AshuDas503/H-CUBE-Smartwatch/images/3D BOTTOM.png

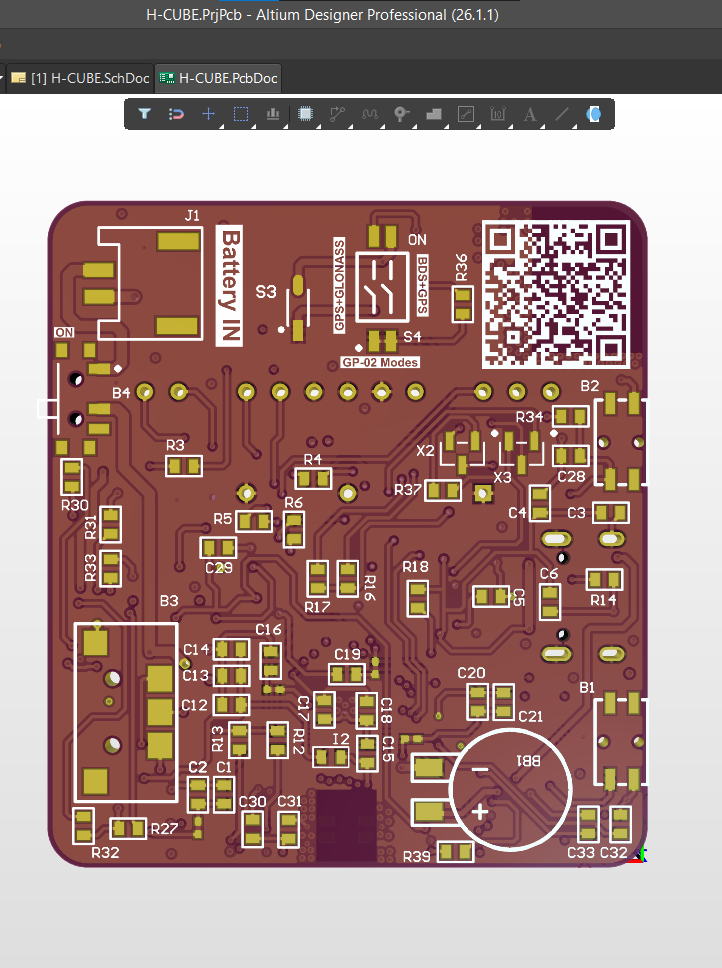
images/3D BOTTOM.png
