AshuDas503/H-CUBE-Smartwatch/images/Layer 1.png

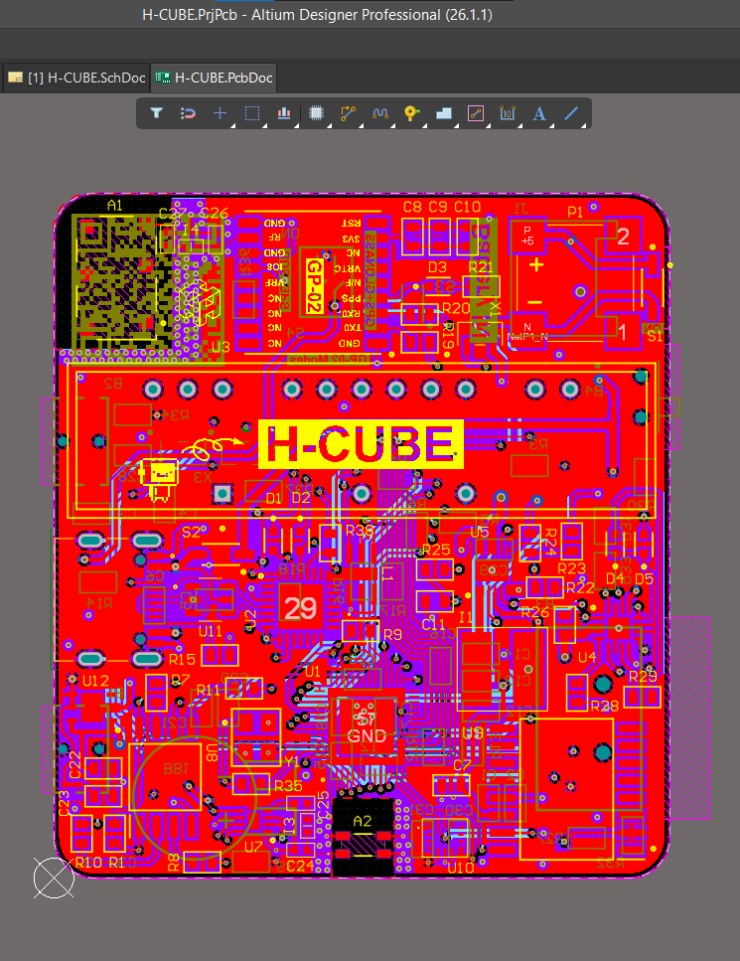
images/Layer 1.png
