AshuDas503/H-CUBE-Smartwatch/images/Layer 2.png

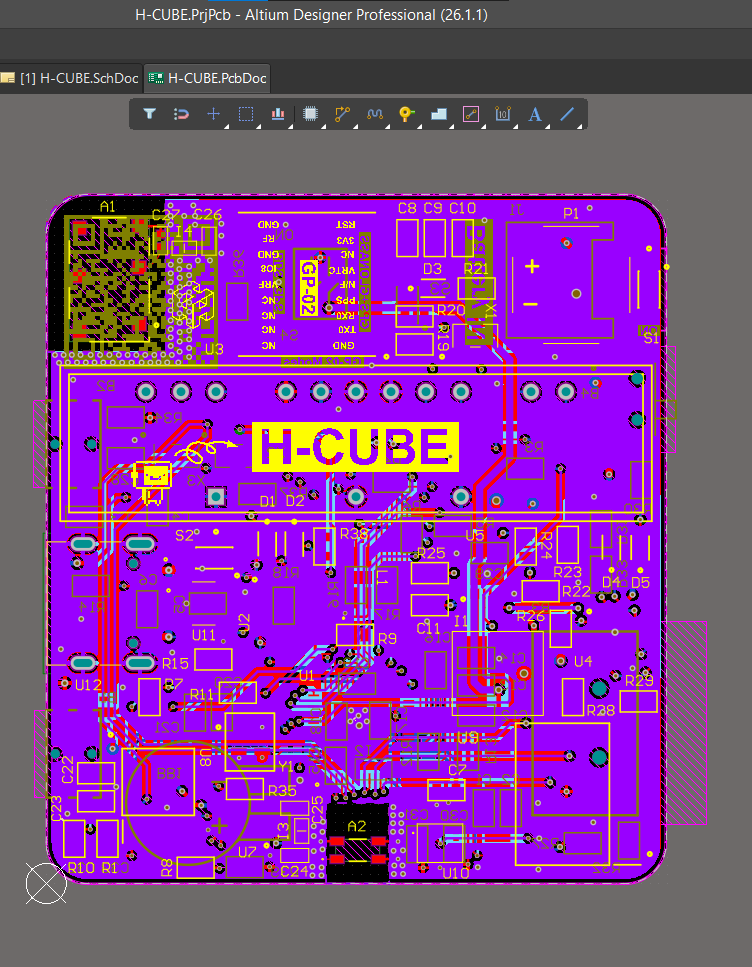
images/Layer 2.png
