AshuDas503/H-CUBE-Smartwatch/images/Layer 3.png

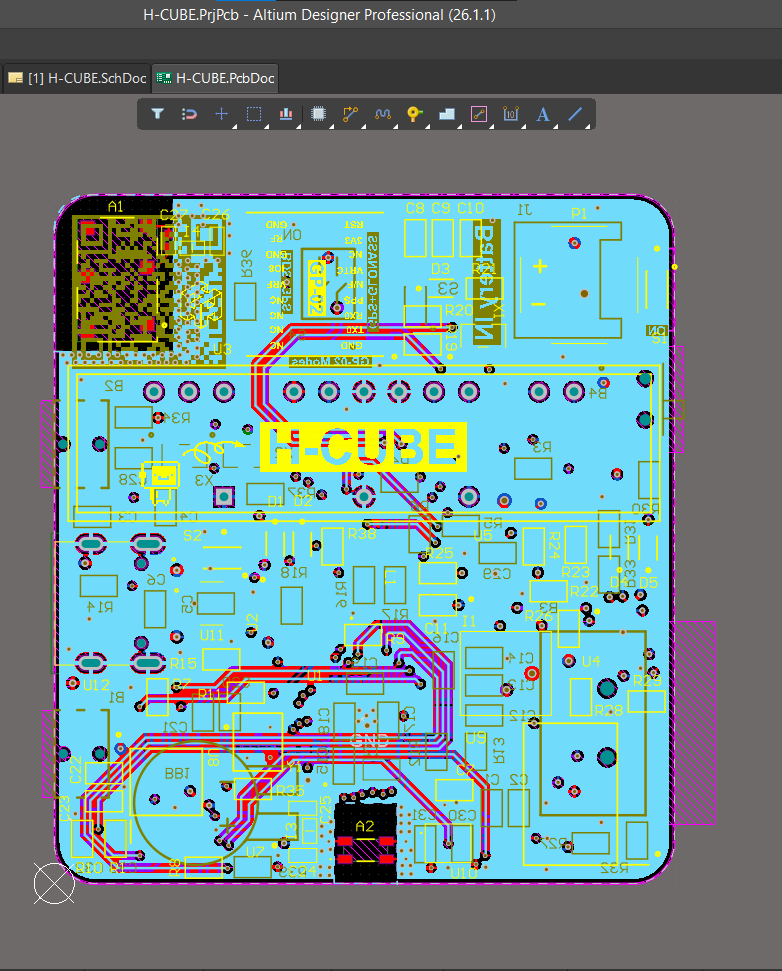
images/Layer 3.png
