AshuDas503/H-CUBE-Smartwatch/images/PCB View2.jpg

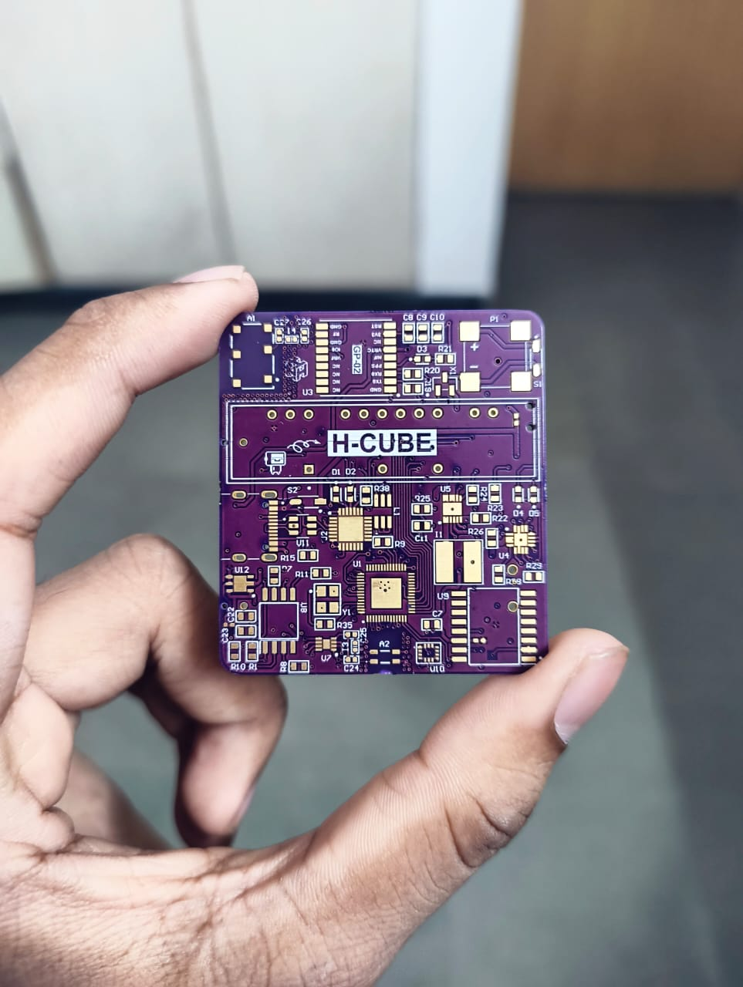
images/PCB View2.jpg
