AshuDas503/H-CUBE-Smartwatch/images/3D view with component Bottom.png

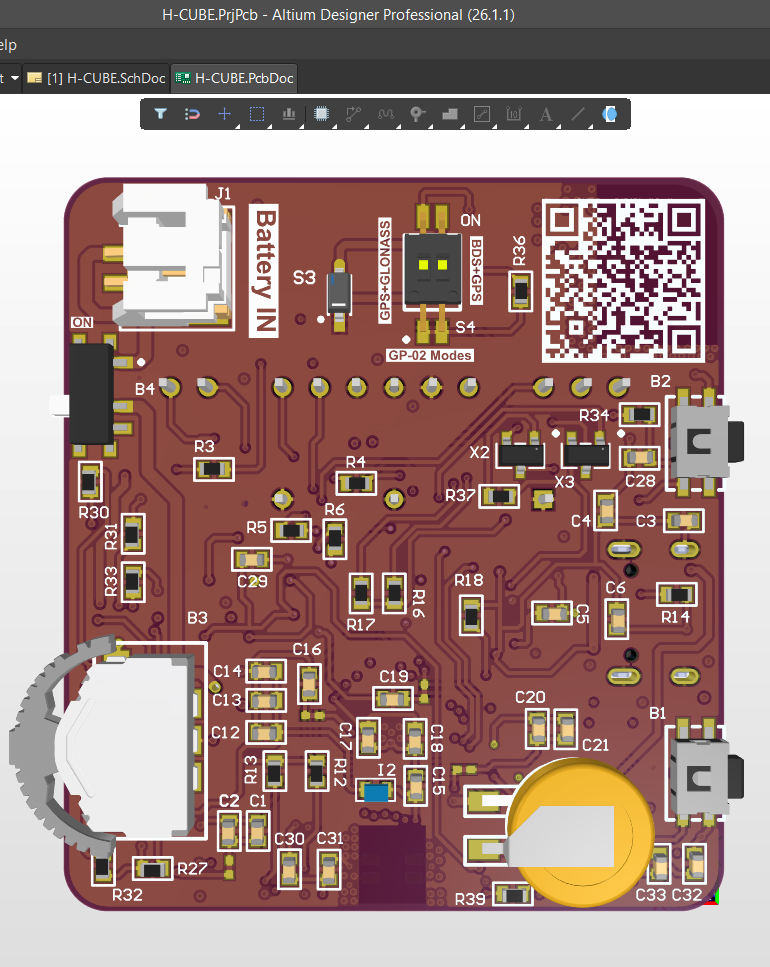
images/3D view with component Bottom.png
