AshuDas503/H-CUBE-Smartwatch/images/3d view with components top.png

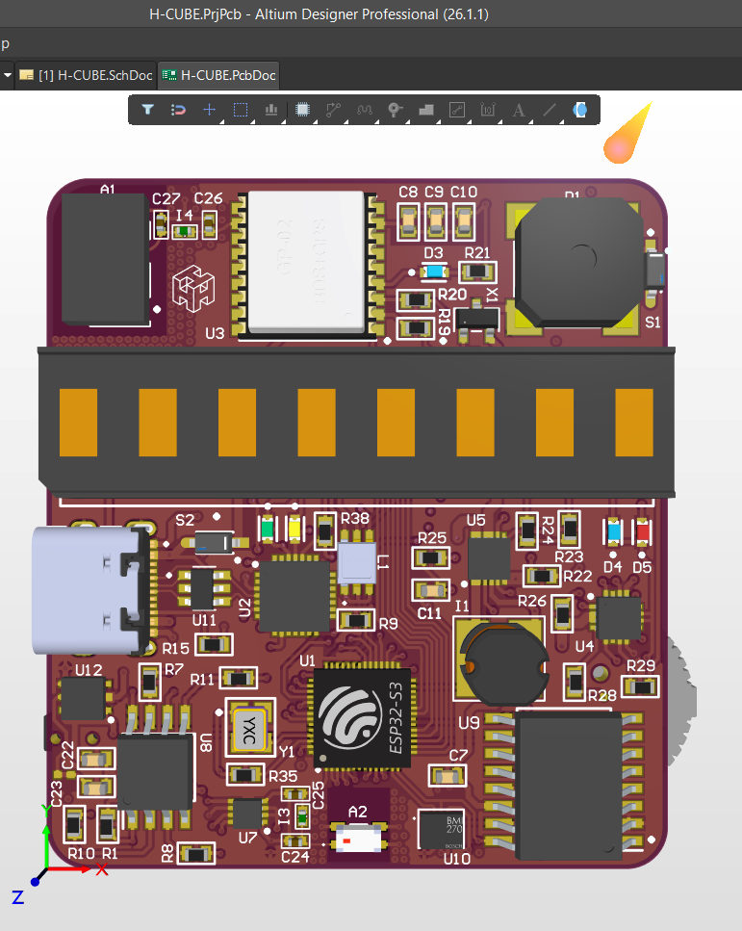
images/3d view with components top.png
